moonfriendsynth/Sack-Lunch-VCO/Sack Lunch VCO.kicad_sch

## KiCad design Sack Lunch VCO.kicad_sch (2023-11-06)

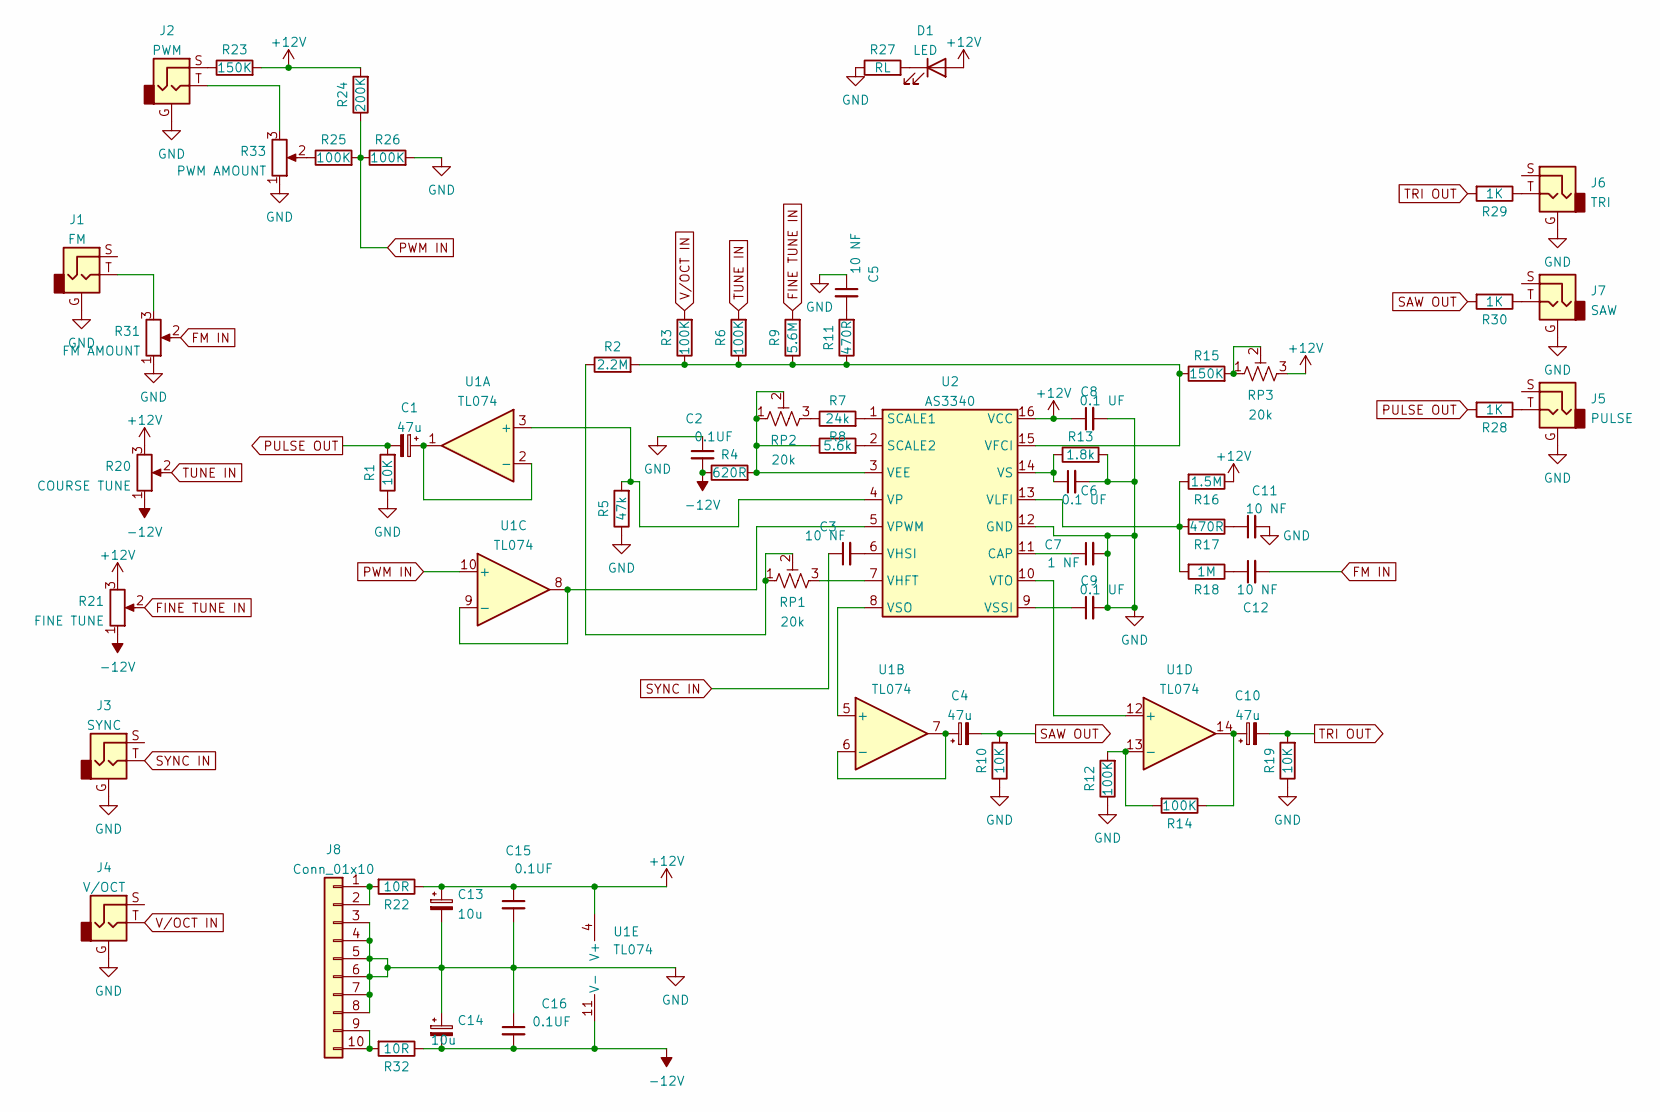
[picture p2: schematic Sack Lunch VCO.kicad_sch]

Parts:
C1, C4, C10: 47u
C2, C15, C16: 0.1UF
C3, C5, C11, C12: 10 NF
C6, C8, C9: 0.1 UF
C7: 1 NF
C13, C14: 10u
D1: LED
J1: FM
J2: PWM
J3: SYNC
J4: V/OCT
J5: PULSE
J6: TRI
J7: SAW
J8: Conn_01x10
R1, R10, R19: 10K
R2: 2.2M
R3, R6, R12, R14, R25, R26: 100K
R4: 620R
R5: 47k
R7: 24k
R8: 5.6k
R9: 5.6M
R11, R17: 470R
R13: 1.8k
R15, R23: 150K
R16: 1.5M
R18: 1M
R20: COURSE TUNE; Potentiometer_Alpha_RD901F-40-00D_Single_Vertical_CircularH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
R21: FINE TUNE; Potentiometer_Alpha_RD901F-40-00D_Single_Vertical_CircularH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
R22, R32: 10R
R24: 200K
R27: RL
R28, R29, R30: 1K
R31: FM AMOUNT; Potentiometer_Alpha_RD901F-40-00D_Single_Vertical_CircularH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
R33: PWM AMOUNT; Potentiometer_Alpha_RD901F-40-00D_Single_Vertical_CircularH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
RP1, RP2, RP3: 20k
U1: TL074
U2: AS3340

Connections:
+12V: C8.1, C13.1, C15.1, D1.2 (A), R16.1, R20.3, R21.3, R22.1, R23.2, R24.2, RP3.3, U1.4 (V+), U2.16 (VCC)
-12V: C2.2, C14.2, C16.2, R4.1, R20.1, R21.1, R32.1, U1.11 (V-)
FINE TUNE IN: R9.2, R21.2
FM IN: C12.2, R31.2
GND: C2.1, C5.1, C6.2, C7.2, C8.2, C9.2, C11.2, C13.2, C14.1, C15.2, C16.1, J1.G, J2.G, J3.G, J4.G, J5.G, J6.G, J7.G, J8.3, J8.4, J8.5, J8.6, J8.7, J8.8, R1.1, R5.1, R10.1, R12.1, R13.2, R19.1, R26.2, R27.1, R31.1, R33.1, U2.12 (GND)
unnamed: C1.1, U1.1, U1.2 (-)
unnamed: C3.2, U2.6 (VHSI)
unnamed: C4.1, U1.6 (-), U1.7
unnamed: C5.2, R11.2
unnamed: C6.1, R13.1, U2.14 (VS)
unnamed: C7.1, U2.11 (CAP)
unnamed: C9.1, U2.9 (VSSI)
unnamed: C10.1, R14.1, U1.14
unnamed: C11.1, R17.1
unnamed: C12.1, R18.1
unnamed: D1.1 (K), R27.2
unnamed: J1.T, R31.3
unnamed: J2.S, R23.1
unnamed: J2.T, R33.3
unnamed: J5.T, R28.1
unnamed: J6.T, R29.1
unnamed: J7.T, R30.1
unnamed: J8.1, J8.2, R22.2
unnamed: J8.9, J8.10, R32.2
unnamed: R2.1, RP1.1, RP1.2
unnamed: R4.2, R8.1, RP2.1, RP2.2, U2.3 (VEE)
unnamed: R5.2, U1.3 (+), U2.4 (VP)
unnamed: R7.1, RP2.3
unnamed: R7.2, U2.1 (SCALE1)
unnamed: R8.2, U2.2 (SCALE2)
unnamed: R2.2, R3.1, R6.1, R9.1, R11.1, R15.1, U2.15 (VFCI)
unnamed: R12.2, R14.2, U1.13 (-)
unnamed: R15.2, RP3.1, RP3.2
unnamed: R16.2, R17.2, R18.2, U2.13 (VLFI)
unnamed: R25.1, R33.2
unnamed: RP1.3, U2.7 (VHFT)
unnamed: U1.5 (+), U2.8 (VSO)
unnamed: U1.8, U1.9 (-), U2.5 (VPWM)
unnamed: U1.12 (+), U2.10 (VTO)
PULSE OUT: C1.2, R1.2, R28.2
PWM IN: R24.1, R25.2, R26.1, U1.10 (+)
SAW OUT: C4.2, R10.2, R30.2
SYNC IN: C3.1, J3.T
TRI OUT: C10.2, R19.2, R29.2
TUNE IN: R6.2, R20.2
V/OCT IN: J4.T, R3.2
